es3649/robo-rally-online/player-client/src/assets/loading/PCB.png

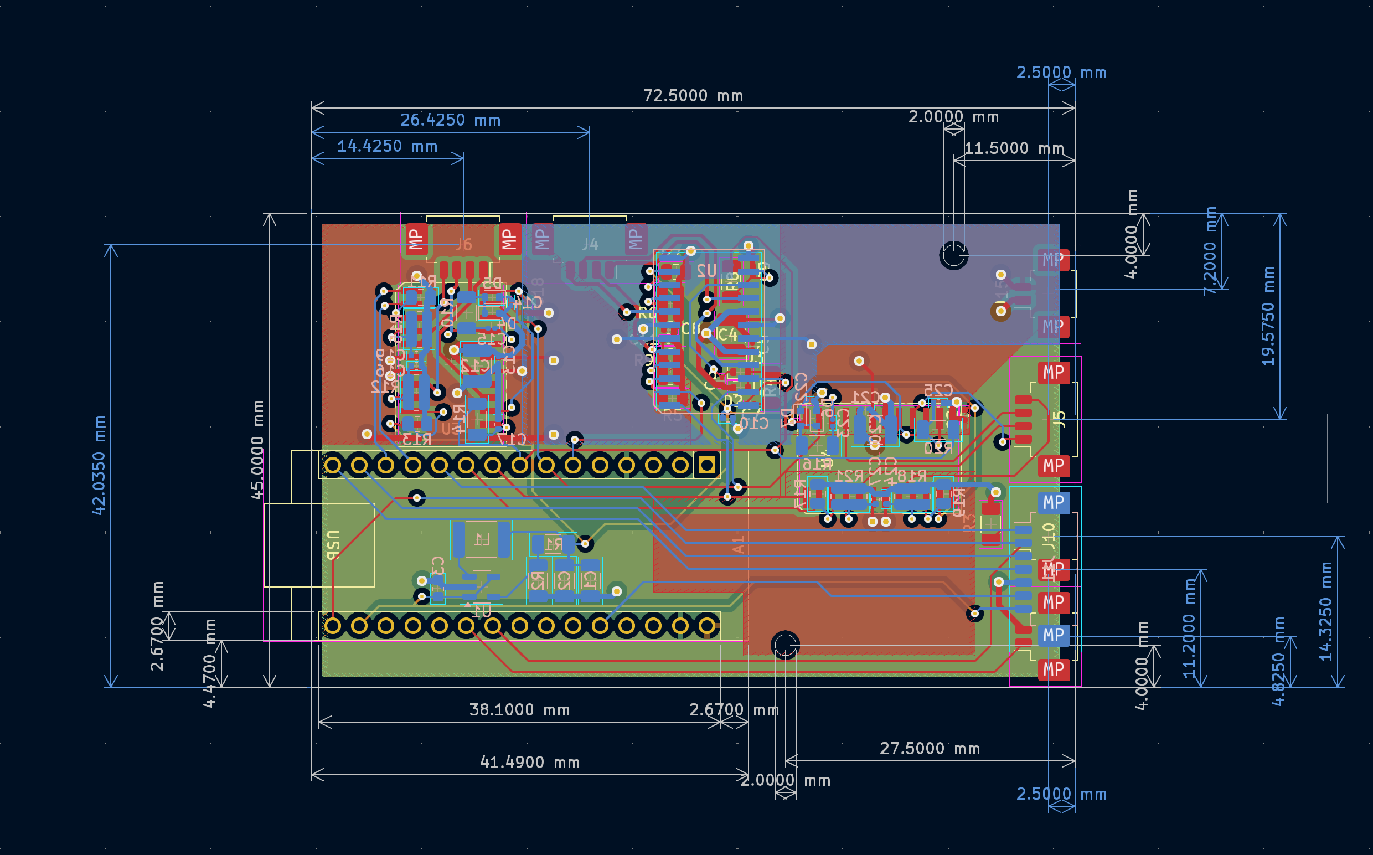
player-client/src/assets/loading/PCB.png
