es3649/robo-rally-online/shared/assets/robot_race1.jpg

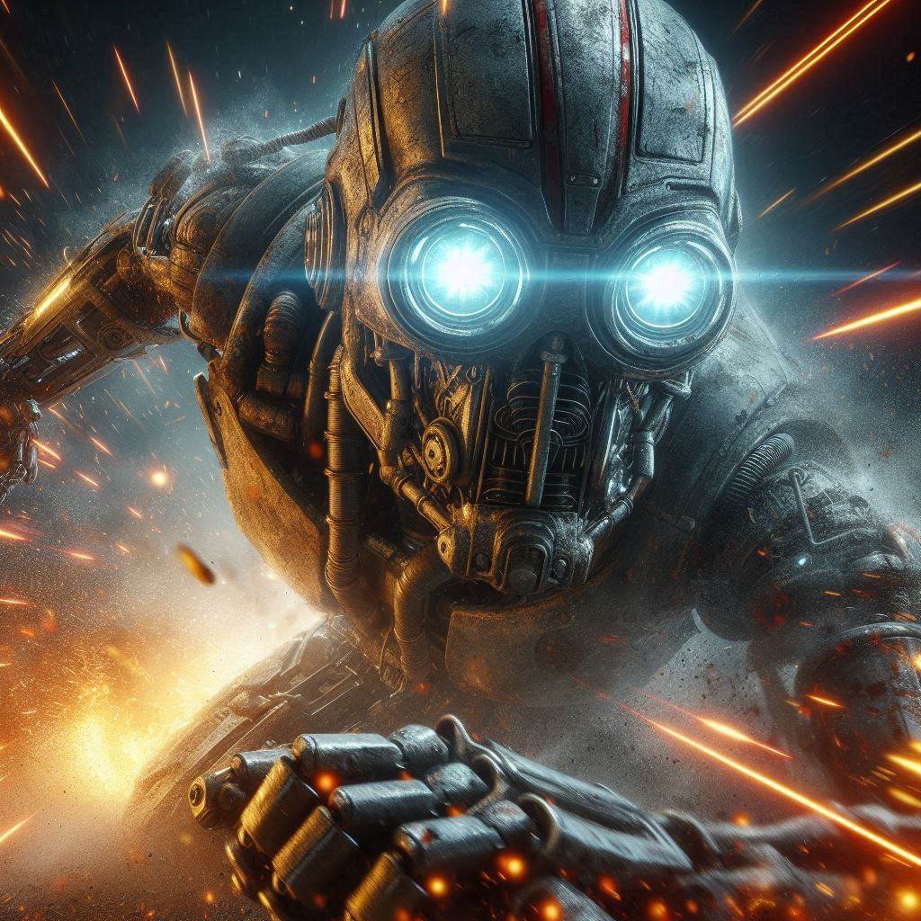
shared/assets/robot_race1.jpg
