es3649/robo-rally-online/bot_drivers/test/BLE/BLE Test Schematic.kicad_sch

## KiCad design bot_drivers/test/BLE/BLE Test Schematic.kicad_sch (2025-02-26)

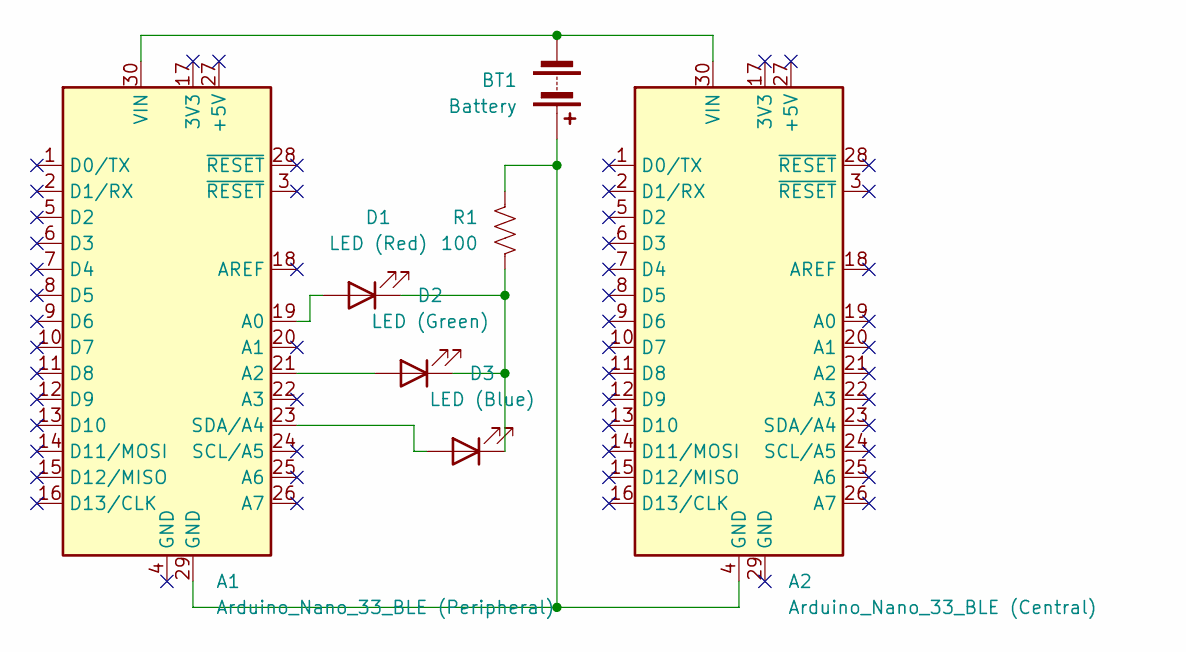
[picture p11: schematic BLE Test Schematic.kicad_sch]

Parts:
A1: Arduino_Nano_33_BLE (Peripheral); Arduino_Nano
A2: Arduino_Nano_33_BLE (Central); Arduino_Nano
BT1: Battery
D1: LED (Red)
D2: LED (Green)
D3: LED (Blue)
R1: 100

Connections:
unnamed: A1.19 (A0), D1.2 (A)
unnamed: A1.21 (A2), D2.2 (A)
unnamed: A1.23 (SDA/A4), D3.2 (A)
unnamed: A1.29 (GND), A2.4 (GND), BT1.1 (+), R1.1
unnamed: A1.30 (VIN), A2.30 (VIN), BT1.2 (-)
unnamed: D1.1 (K), D2.1 (K), D3.1 (K), R1.2
