es3649/robo-rally-online/bot_drivers/test/L6208_test/L6208 Test Schematic.kicad_sch

## KiCad design bot_drivers/test/L6208_test/L6208 Test Schematic.kicad_sch (2025-02-26)

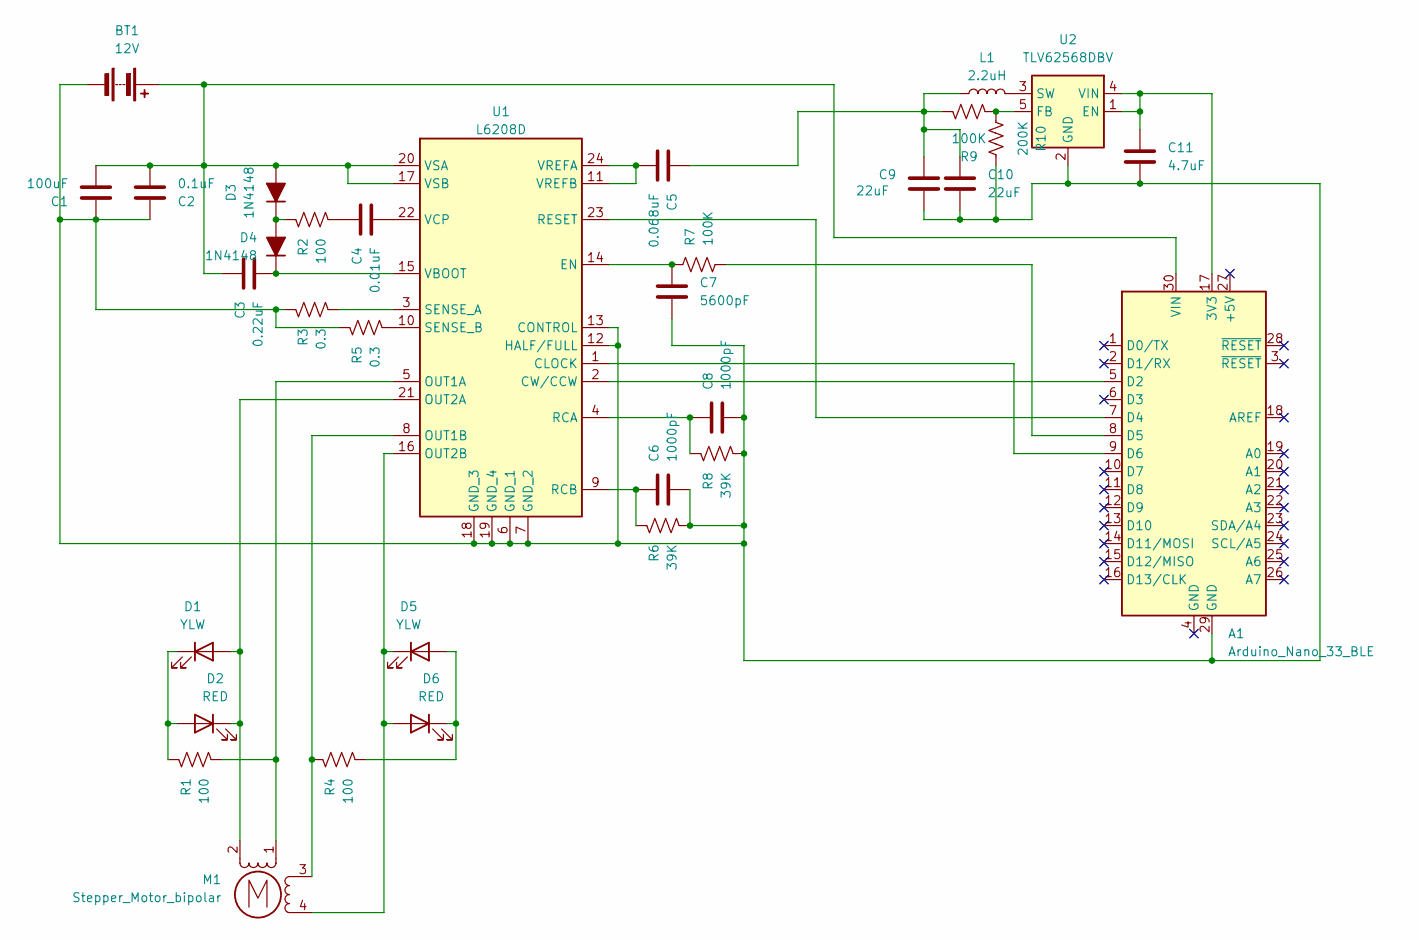
[picture p12: schematic L6208 Test Schematic.kicad_sch]

Parts:
A1: Arduino_Nano_33_BLE; Arduino_Nano
BT1: 12V; JWT_A3963_1x02_P3.96mm_Vertical
C1: 100uF; C_1210_3225Metric
C2: 0.1uF; C_0201_0603Metric_Pad0.64x0.40mm_HandSolder
C3: 0.22uF; C_0201_0603Metric
C4: 0.01uF; C_0201_0603Metric
C5: 0.068uF; C_0402_1005Metric
C6, C8: 1000pF; C_0402_1005Metric
C7: 5600pF; C_0402_1005Metric
C9, C10: 22uF; C_1206_3216Metric
C11: 4.7uF; C_0603_1608Metric
D1, D5: YLW
D2, D6: RED
D3, D4: 1N4148; D_SOD-523
L1: 2.2uH; L_1812_4532Metric
M1: Stepper_Motor_bipolar; Molex_Pico-Clasp_501331-0407_1x04-1MP_P1.00mm_Vertical
R1, R2, R4: 100; R_1206_3216Metric
R3, R5: 0.3; R_0805_2012Metric
R6, R8: 39K; R_0612_1632Metric
R7, R9: 100K; R_1206_3216Metric
R10: 200K; R_1206_3216Metric
U1: L6208D; ST_PowerSSO-24_SlugUp
U2: TLV62568DBV; SOT-23-5

Connections:
unnamed: A1.5 (D2), U1.2 (CW/CCW)
unnamed: A1.7 (D4), U1.23 (RESET)
unnamed: A1.8 (D5), R7.2
unnamed: A1.9 (D6), U1.1 (CLOCK)
unnamed: A1.17 (3V3), C11.1, U2.1 (EN), U2.4 (VIN)
unnamed: A1.29 (GND), BT1.2 (-), C1.1, C2.1, C6.2, C7.2, C8.2, C9.1, C10.1, C11.2, R3.1, R5.1, R6.2, R8.2, R10.1, U1.6 (GND_1), U1.7 (GND_2), U1.12 (HALF/FULL), U1.13 (CONTROL), U1.18 (GND_3), U1.19 (GND_4), U2.2 (GND)
unnamed: A1.30 (VIN), BT1.1 (+), C1.2, C2.2, C3.1, D3.2 (A), U1.17 (VSB), U1.20 (VSA)
unnamed: C3.2, D4.1 (K), U1.15 (VBOOT)
unnamed: C4.1, R2.2
unnamed: C4.2, U1.22 (VCP)
unnamed: C5.2, U1.11 (VREFB), U1.24 (VREFA)
unnamed: C6.1, R6.1, U1.9 (RCB)
unnamed: C7.1, R7.1, U1.14 (EN)
unnamed: C8.1, R8.1, U1.4 (RCA)
unnamed: C5.1, C9.2, C10.2, L1.1, R9.2
unnamed: D1.1 (K), D2.2 (A), R1.1
unnamed: D1.2 (A), D2.1 (K), M1.2 (-), U1.21 (OUT2A)
unnamed: D3.1 (K), D4.2 (A), R2.1
unnamed: D5.1 (K), D6.2 (A), M1.4, U1.16 (OUT2B)
unnamed: D5.2 (A), D6.1 (K), R4.2
unnamed: L1.2, U2.3 (SW)
unnamed: M1.1, R1.2, U1.5 (OUT1A)
unnamed: M1.3, R4.1, U1.8 (OUT1B)
unnamed: R3.2, U1.3 (SENSE_A)
unnamed: R5.2, U1.10 (SENSE_B)
unnamed: R9.1, R10.2, U2.5 (FB)
