es3649/robo-rally-online/bot_drivers/test/rfid_test/rfid Test Schematic.kicad_sch

## KiCad design bot_drivers/test/rfid_test/rfid Test Schematic.kicad_sch (2025-02-26)

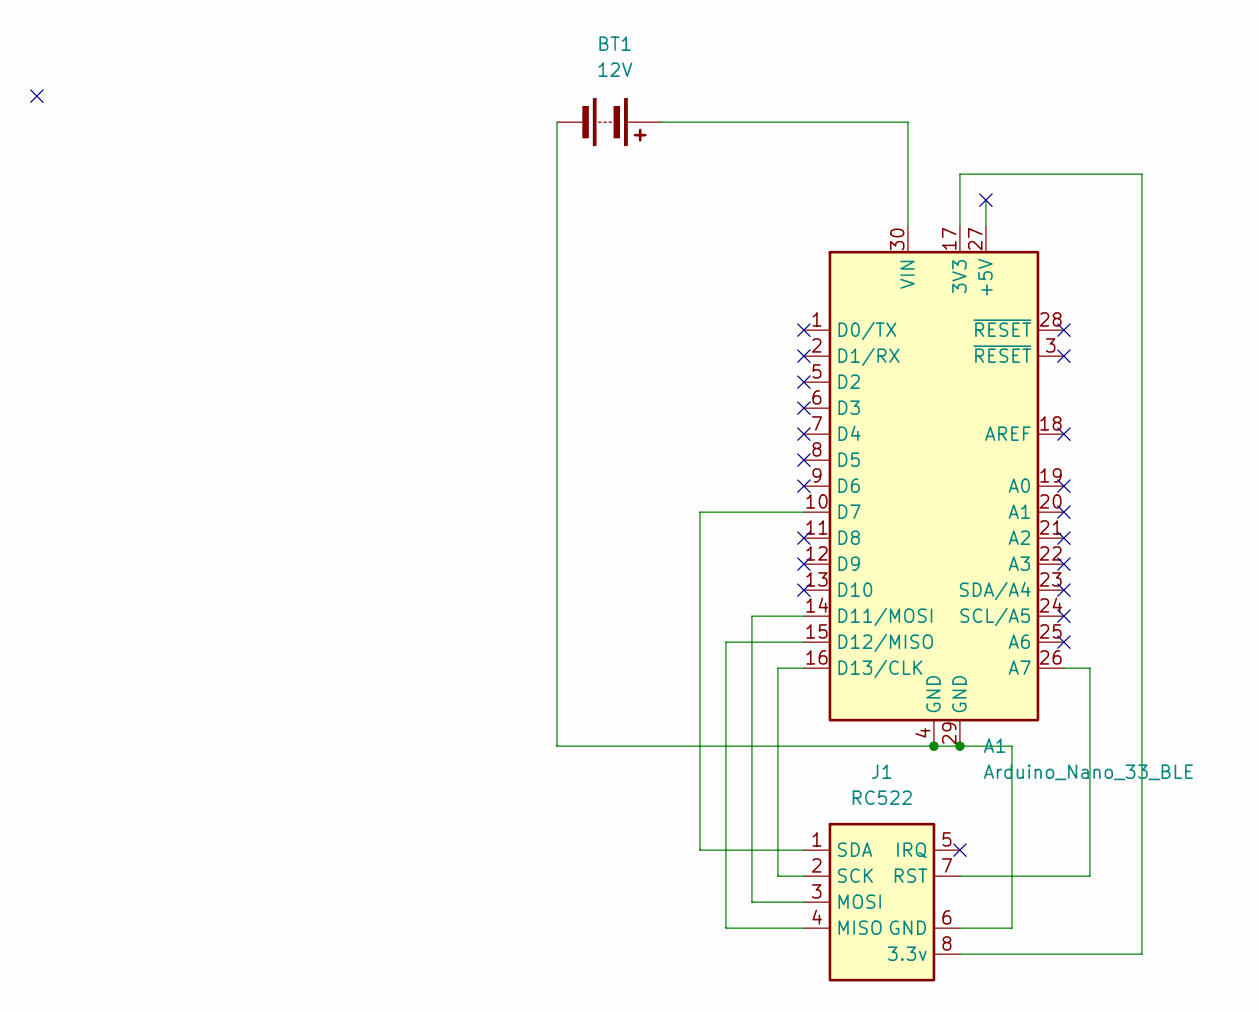
[picture p13: schematic rfid Test Schematic.kicad_sch]

Parts:
A1: Arduino_Nano_33_BLE; Arduino_Nano
BT1: 12V; JWT_A3963_1x02_P3.96mm_Vertical
J1: RC522

Connections:
unnamed: A1.10 (D7), J1.1 (SDA)
unnamed: A1.14 (D11/MOSI), J1.3 (MOSI)
unnamed: A1.15 (D12/MISO), J1.4 (MISO)
unnamed: A1.16 (D13/CLK), J1.2 (SCK)
unnamed: A1.17 (3V3), J1.8 (3.3v)
unnamed: A1.26 (A7), J1.7 (RST)
unnamed: A1.4 (GND), A1.29 (GND), BT1.2 (-), J1.6 (GND)
unnamed: A1.30 (VIN), BT1.1 (+)
