es3649/robo-rally-online/bot_drivers/test/rfid_test/rfid_test.ino

#include <SPI.h>
#include <MFRC522.h>

#define SS_PIN 7
#define RST_PIN 6

MFRC522 rfid(SS_PIN, RST_PIN);

byte nuidPICC[4];

void setup() {
  // put your setup code here, to run once:
  Serial.begin(9600);
  SPI.begin();
  rfid.PCD_Init();

  Serial.println("READY TO SCAN");

}

void loop() {
  // put your main code here, to run repeatedly:
  if (!rfid.PICC_IsNewCardPresent()) {
    return;
  }

  if (!rfid.PICC_ReadCardSerial()) {
    return;
  }

  Serial.print("PICC type: ");
  MFRC522::PICC_Type piccType = rfid.PICC_GetType(rfid.uid.sak);
  Serial.println(rfid.PICC_GetTypeName(piccType));

  if (piccType != MFRC522::PICC_TYPE_MIFARE_MINI &&
      piccType != MFRC522::PICC_TYPE_MIFARE_1K &&
      piccType != MFRC522::PICC_TYPE_MIFARE_4K)
  {
    Serial.println("Your tag is not of type MIFARE Classic.");
    return;
  }

  if (rfid.uid.uidByte[0] != nuidPICC[0] || 
    rfid.uid.uidByte[1] != nuidPICC[1] || 
    rfid.uid.uidByte[2] != nuidPICC[2] || 
    rfid.uid.uidByte[3] != nuidPICC[3] ) {
    Serial.println(F("A new card has been detected."));

    // Store NUID into nuidPICC array
    for (byte i = 0; i < 4; i++) {
      nuidPICC[i] = rfid.uid.uidByte[i];
    }
   
    Serial.println(F("The NUID tag is:"));
    Serial.print(F("In hex: "));
    printHex(rfid.uid.uidByte, rfid.uid.size);
    Serial.println();
    Serial.print(F("In dec: "));
    printDec(rfid.uid.uidByte, rfid.uid.size);
    Serial.println();
  }
  else Serial.println(F("Card read previously."));

  // Halt PICC
  rfid.PICC_HaltA();

  // Stop encryption on PCD
  rfid.PCD_StopCrypto1();
}


/**
 * Helper routine to dump a byte array as hex values to Serial. 
 */
void printHex(byte *buffer, byte bufferSize) {
  for (byte i = 0; i < bufferSize; i++) {
    Serial.print(buffer[i] < 0x10 ? " 0" : " ");
    Serial.print(buffer[i], HEX);
  }
}

/**
 * Helper routine to dump a byte array as dec values to Serial.
 */
void printDec(byte *buffer, byte bufferSize) {
  for (byte i = 0; i < bufferSize; i++) {
    Serial.print(' ');
    Serial.print(buffer[i], DEC);
  }
}
